htegeth/helmlicht/doc/FrontSide.jpg

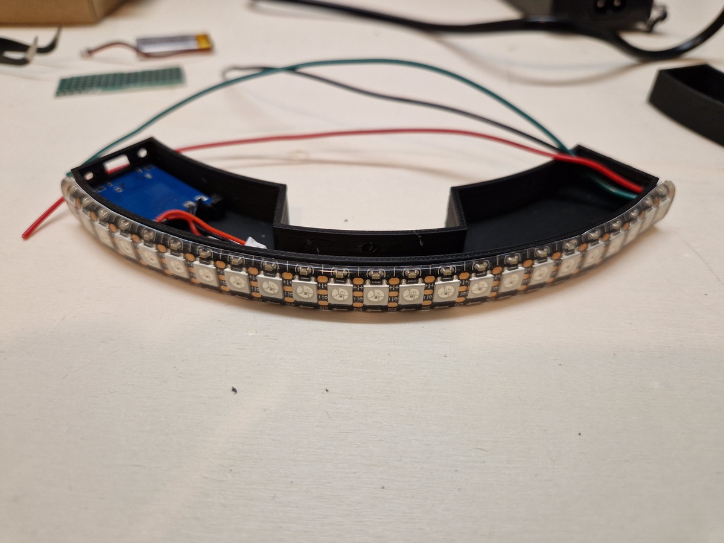
doc/FrontSide.jpg
