htegeth/helmlicht/src/BlinkMuster.cpp

#include <BlinkMuster.h>

BlinkMuster::BlinkMuster()
{
}

void BlinkMuster::setLeds(CRGB *leds)
{
    this->leds = leds;
}

void BlinkMuster::setBlinkLeft()
{
    int8_t blinkStartPosition = NUM_LEDS - LED_FRAGMENT;
    if (iPos < blinkStartPosition || iPos == NUM_LEDS)
    {
        FastLED.clear();
        FastLED.show();
        iPos = blinkStartPosition;
        tone(TONE_PIN, 150, 200);
        delay(700);
    }
    leds[iPos++].setHue(HUE_ORANGE);
    FastLED.show();
    delay(100);
}

void BlinkMuster::setBlinkRight()
{
    if (iPos >= LED_FRAGMENT || iPos < 0)
    {
        FastLED.clear();
        FastLED.show();
        delay(150);
        iPos = RIGHT_BEGIN;
        tone(TONE_PIN, 50, 200);
        delay(700);
    }
    leds[iPos--].setHue(HUE_ORANGE);
    FastLED.show();
    delay(100);
}

void BlinkMuster::drawComet()
{
    hue += deltaHue;
    iPos += iDirection;
    if (iPos == (NUM_LEDS - COMET_SIZE) || iPos == 0)
        iDirection *= -1;

    for (int i = 0; i < COMET_SIZE; i++)
        leds[iPos + i].setHue(hue);

    // Zufälliges Ausblenden der LEDs
    for (int j = 0; j < NUM_LEDS; j++)
        if (random(10) > 5)
            leds[j] = leds[j].fadeToBlackBy(FADEAMT);
    FastLED.show();
    delay(60);
}

void BlinkMuster::drawKitt()
{    
    //Reset, falls die Positionswerte und die Direction nicht mehr passen
    if (iPos> NUM_LEDS || iPos< 0 || abs(iDirection)!= 1)
    {
        iPos=0;
        iDirection=1;
    }
    iPos += iDirection;
    if (iPos == (NUM_LEDS - 1) || iPos == 0)
        iDirection *= -1;

    FastLED.clear();
    leds[iPos].setHue(HUE_RED).fadeLightBy(0);
    if ((iPos + 1) < NUM_LEDS)
         leds[iPos + 1].setHue(HUE_RED).fadeToBlackBy(150);
    leds[iPos - 1].setHue(HUE_RED).fadeToBlackBy(150);
    FastLED.show();
    delay(43);
}

void BlinkMuster::drawHollywood()
{
    (marqueeHue < 255) ? marqueeHue+=4:0;
    byte newHue = marqueeHue;
    
    CRGB c;
    for (int i = 0; i < (NUM_LEDS + 1) / 2; i ++)
    {   
        leds[i]=  c.setHue(newHue);
        leds[NUM_LEDS - 1 - i]=  leds[i];
        (newHue < 255) ? newHue+=8: newHue=0;
    }    
    leds[random(NUM_LEDS)].setColorCode(CRGB::White).maximizeBrightness();   
    FastLED.show();
    delay(50);          
}

void BlinkMuster::drawFullRed(uint8_t brightness){
    for (int i=0; i< NUM_LEDS; i++)
    {
        leds[i] = CRGB::Red;
        leds[i].fadeLightBy(brightness);
    }
    FastLED.show();
    delay(50);  
}
